rodrigocadiz/analog_ring_mod/LTSpice paper simulations/Simulaciones paper/AD633.asc

C1: cap; 0.1µF
C2: cap; 0.1µF
V1: voltage; 12
V2: voltage; 12
V3: voltage; INPUT 1
V4: voltage; INPUT 2
Named nets: VDD, VSS, 0, W, X2, Y2, Z, X1, Y1
AD633
= (X1 - X2)(Y1 - Y2)*0.1 + Z
POWER SUPPLY
MULTIPLIER CIRCUIT WITH AD633
Z IS AN OPTIONAL OFFSET
IN THIS CASE: Z = 0
