rodrigocadiz/analog_ring_mod/LTSpice paper simulations/Simulaciones paper/Draft1.asc

C1: cap; 3.84f
C2: cap; 1.95p
C3: cap; 0.01µF
C4: cap; 470p
C5: cap; 220p
C6: cap; 0.01µF
C7: cap; 60p
L1: ind; 412m
Q1: npn; BC547B
R1: res; 68
R2: res; 100
R3: res; 15k
R4: res; 2.2k
R5: res; 2.56k
R6: res; 5.1k
V1: voltage; 12
Named nets: XTAL_A, XTAL_B, VDD, 0, OUT
.tran 0.01 uic
