rodrigocadiz/analog_ring_mod/LTSpice paper simulations/Simulaciones paper/Diodos y opamps/Draft1.asc

D1: diode; 1N4148
D2: diode; 1N4148
D3: diode; 1N4148
D4: diode; 1N4148
R1: res; 1k
R2: res; 1k
R3: res; 1k
R4: res; 1k
R5: res; 1k
R6: res; 1k
R7: res; 1k
R8: res; 1k
R9: res; 1k
R10: res; 1k
R11: res; 1k
R12: res; 1k
U1: opamp
U2: opamp
U3: opamp
U4: opamp
V1: voltage; SINE(0 5 100)
V2: voltage; SINE(0 5 10)
Named nets: 0, VOUT
.lib opamp.sub
.tran 1
Four quadrant multiplier with 1N4148 diodes
