rodrigocadiz/analog_ring_mod/LTSpice paper simulations/Simulaciones paper/NMOS y opamps/Draft2.asc

C1: cap; 47µF
C2: cap; 47µF
C3: cap; 47µF
C4: cap; 47µF
M1: nmos; 2N7002
M2: nmos; 2N7002
M3: nmos; 2N7002
M4: nmos; 2N7002
R1: res; 100k
R2: res; 100k
R3: res; 100k
R4: res; 5.6k
R5: res; 5.6k
R6: res; 100k
R7: res; 100k
R8: res; 24k
R9: res; 1k
R10: res; 24k
R11: res; 1k
R12: res; 12k
R13: res; 4.7k
R14: res; 4.7k
R15: res; 12k
R16: res; 100k
R17: res; 100k
R18: res; 100k
R19: res; 5.6k
R20: res; 5.6k
R21: res; 100k
R22: res; 100k
R23: res; 24k
R24: res; 1k
R25: res; 24k
R26: res; 1k
R27: res; 12k
R28: res; 4.7k
R29: res; 4.7k
R30: res; 12k
R31: res; 47K
R32: res; 47K
R33: res; 4.7K
R34: res; 47K
R35: res; 47K
R36: res; 4.7K
R37: res; 4.7k
R38: res; 9.1k
R39: res; 1k
R40: res; 9.1k
R41: res; 1k
R42: res; 1k
R43: res; 1k
U1: LT1001
U2: LT1001
U3: LT1001
U4: LT1001
U5: LT1001
U6: LT1001
U7: LT1001
U8: LT1001
V1: voltage; SINE(0 0.5 50)
V2: voltage; SINE(0 0.5 440)
V3: voltage; 12
V4: voltage; 12
Named nets: VO1, 0, VDD, VSS, VA, VO2, VB, INPUT1, INPUT2, OUTPUT
.tran 0 0.1 0
.lib opamp.sub
-A-B
-A+B
Four quadrant multiplier using NMOS and opamps
