rodrigocadiz/analog_ring_mod/LTSpice paper simulations/Simulaciones paper/Transformador y diodos/Draft3.asc

D1: schottky; 1N5817
D2: schottky; 1N5817
D3: schottky; 1N5817
D4: schottky; 1N5817
L1: ind2; ""
L2: ind2; ""
L3: ind2; ""
L4: ind2; ""
L5: ind2; ""
L6: ind2; ""
R1: res
V1: voltage; ""
V2: voltage; ""
Named nets: 0, OUTPUT
x(t)
h(t)
Typical schemathics of a ring modulator using diodes and transformers
